rgaines19/Connect4/Connect_4/STL/C4_Gate.STL

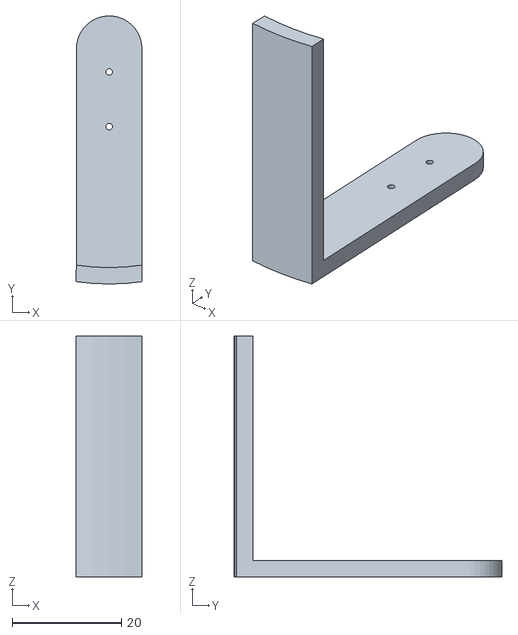
[picture p28: CAD file, 2020-02-01]
Connect_4/STL/C4_Gate.STL
12.1 x 49.0 x 44.0
