rgaines19/Connect4/Connect_4/STL/C4_Chip_Ramp.STL

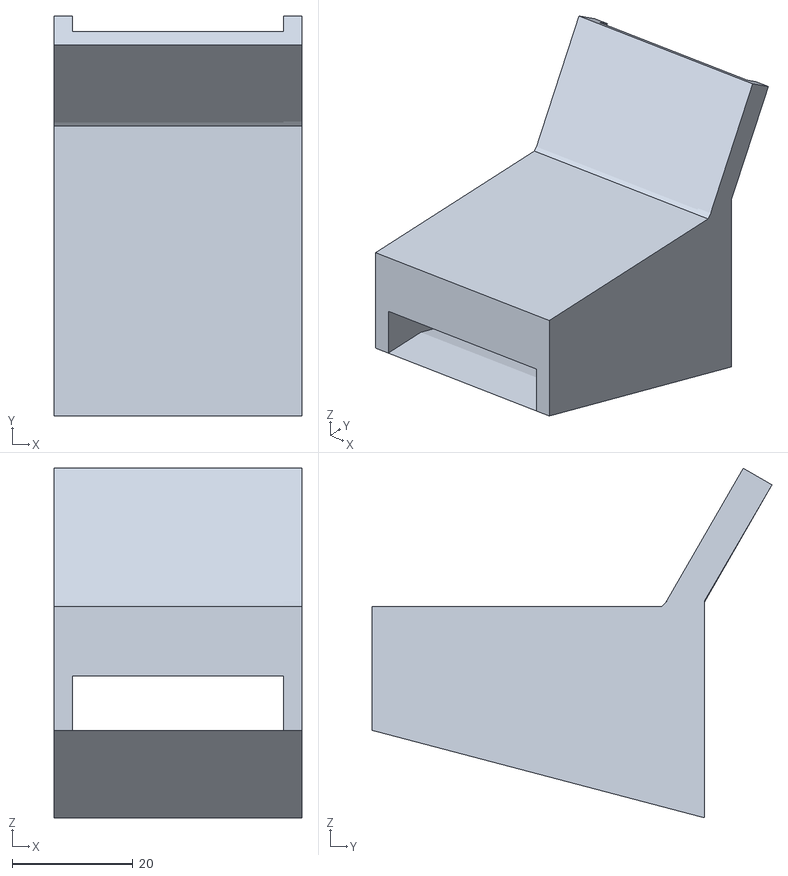
[picture p29: CAD file, 2020-02-01]
Connect_4/STL/C4_Chip_Ramp.STL
41.0 x 66.2 x 57.9
