rgaines19/Connect4/Connect_4/STL/Double_sided.STL

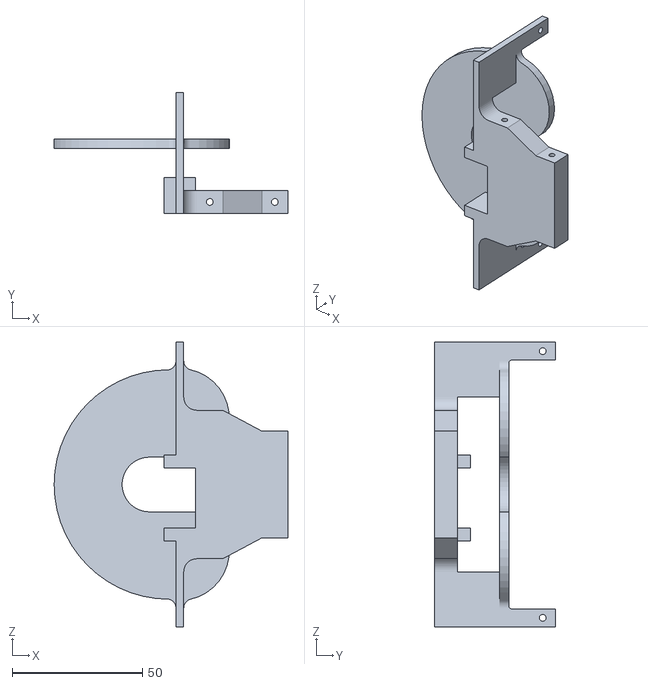
[picture p30: CAD file, 2020-02-01]
Connect_4/STL/Double_sided.STL
89.7 x 46.6 x 109.4
