rgaines19/Connect4/Connect_4/STL/Double_sided_THICK.STL

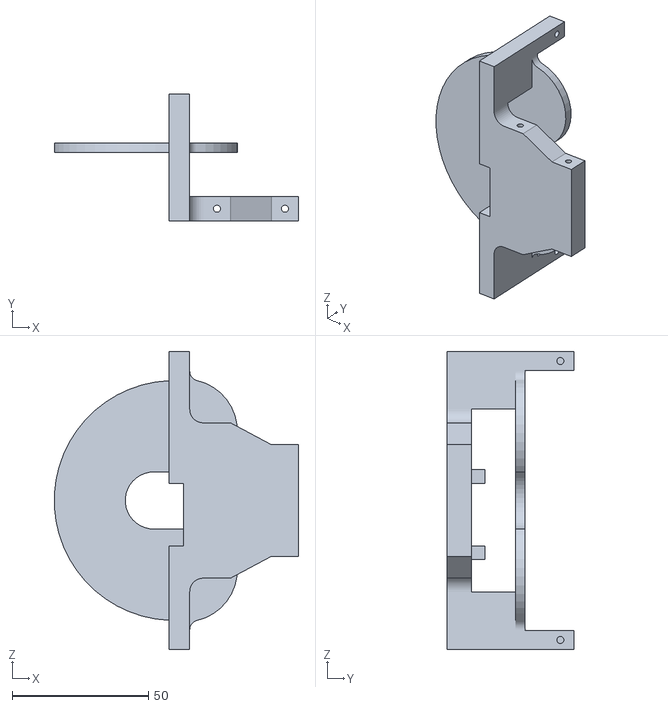
[picture p31: CAD file, 2020-02-01]
Connect_4/STL/Double_sided_THICK.STL
89.6 x 46.6 x 109.4
