rgaines19/Connect4/Connect_4/STL/C4_Halfpipe.STL

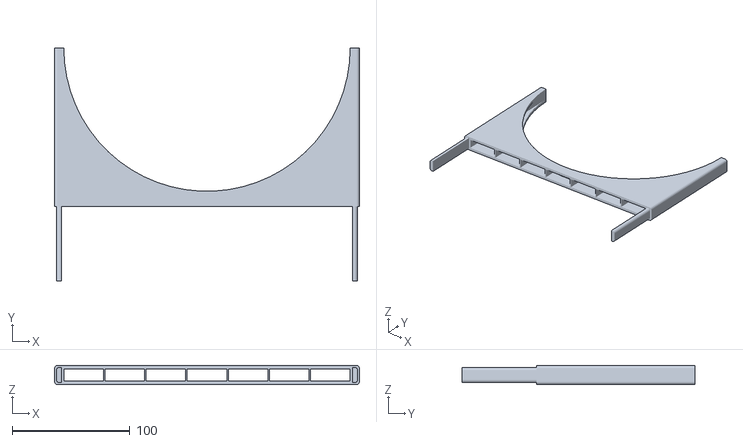
[picture p32: CAD file, 2020-02-01]
Connect_4/STL/C4_Halfpipe.STL
259.6 x 198.1 x 16.3
