rgaines19/Connect4/Connect_4/STL/C4_Halfpipe Leg.STL

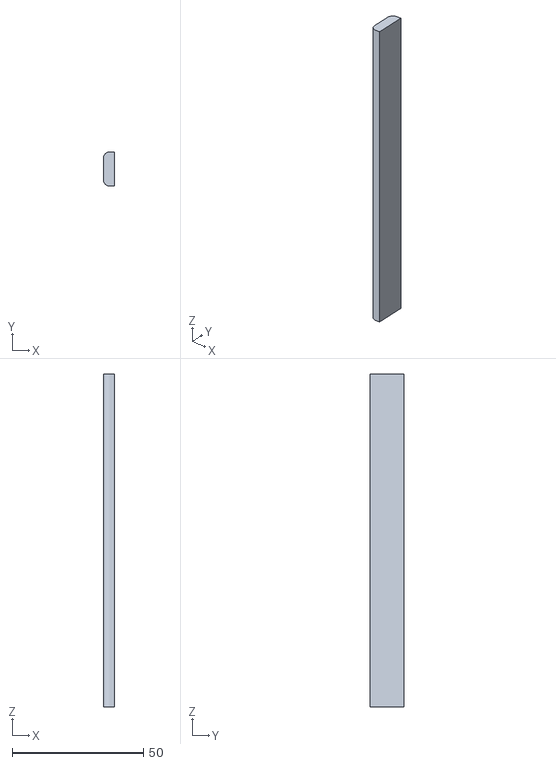
[picture p33: CAD file, 2020-02-01]
Connect_4/STL/C4_Halfpipe Leg.STL
4.38 x 13.1 x 127.0
