rgaines19/Connect4/Connect_4/STL/C4_Extractor.STL

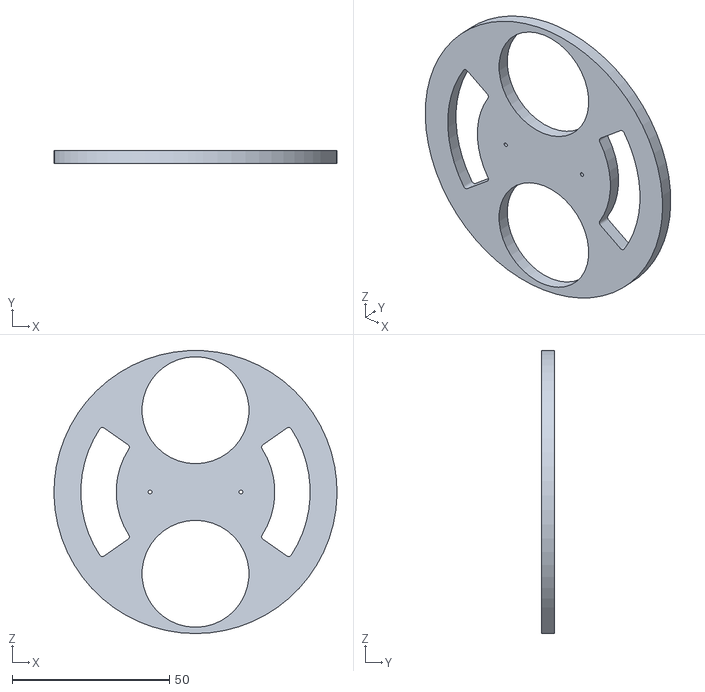
[picture p34: CAD file, 2020-02-01]
Connect_4/STL/C4_Extractor.STL
90.0 x 4.00 x 90.0
