rgaines19/Connect4/Connect_4/STL/C4_Chute_3.STL

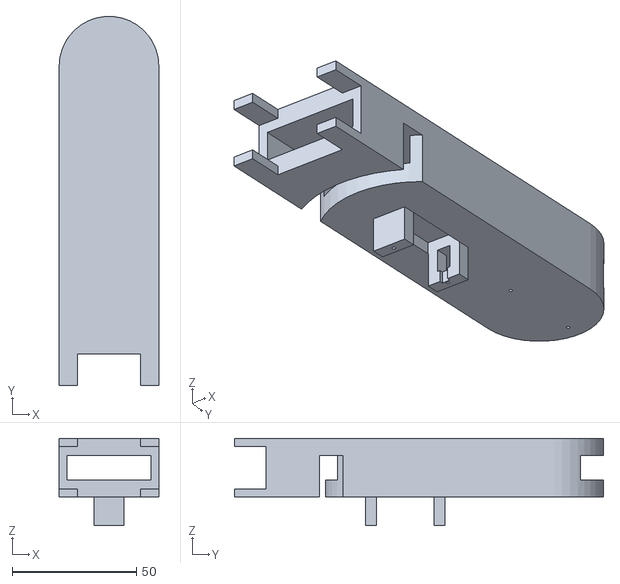
[picture p35: CAD file, 2020-02-01]
Connect_4/STL/C4_Chute_3.STL
40.1 x 148.2 x 35.0
