rgaines19/Connect4/Connect_4/STL/C4_Halfpipe_without_legs.STL

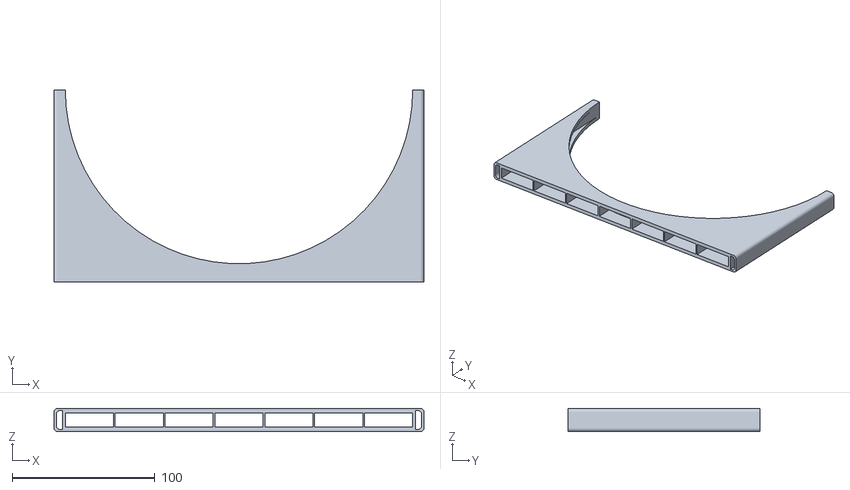
[picture p36: CAD file, 2020-02-01]
Connect_4/STL/C4_Halfpipe_without_legs.STL
259.6 x 134.6 x 16.3
